rmdocherty/CPL-Imager/rotator.py

#!/usr/bin/env python3
# -*- coding: utf-8 -*-
"""
Created on Fri Aug  6 14:33:00 2021

@author: ronan
"""
#from pyftdi.ftdi import Ftdi
#import pyftdi.serialext
from time import sleep
import serial
from math import floor

PULSES_PER_DEGREE = 262144 / 360 #defined in docs
OFFSET_DEGREES = 1.7578125
#old values, H=11.7, V=60.7
HORIZONTAL = 11.7
VERTICAL = 60.7

class Rotator():
    """
    Rotator.

    Class to interface with ELL14 Thorlabs piezo rotation mount. Assumes the
    use of an R232 interface over a USB cable so can use pySerial. Docs says to
    just send ASCII strings for commands to use Serial.write().
    NB MUST TYPE "sudo chmod 666 /dev/ttyUSB0" to get permission to run.
    """

    def __init__(self, port): #might need to add flushing and setting params
        self.rot_count = 0
        connected = False
        try:
            #can just use pyserial to interface though may need to download drivers if on windows
            self._port = port #serial.Serial(port, baudrate=9600) #port='ftdi://ftdi:ft-x:DK0AJJZI/1'
            connected = True
        except Exception as error:
            print(f"Error: {error}, please supply a port.")
        if connected:
            sleep(0.05)
            self._port.reset_input_buffer()
            self._port.reset_output_buffer()
            sleep(0.05)
            self._home_motor() #reset pos
            self.set_jog_90()
            #self.rotate_to_angle(HORIZONTAL) #reset pos

    def _send_command(self, command, data=""):
        """
        Command structure is as follows:
            _____________________________________________________________________________________________
            |                    3 byte header            |                 8 byte data (optional)      |
            | 1 byte motor address (0-A) | 2 byte mneomic |       Hex number encoded as ASCII byte      |
            ¯¯¯¯¯¯¯¯¯¯¯¯¯¯¯¯¯¯¯¯¯¯¯¯¯¯¯¯¯¯¯¯¯¯¯¯¯¯¯¯¯¯¯¯¯¯¯¯¯¯¯¯¯¯¯¯¯¯¯¯¯¯¯¯¯¯¯¯¯¯¯¯¯¯¯¯¯¯¯¯¯¯¯¯¯¯¯¯¯¯¯¯¯
        I just use default motor address (0) - but no real justification.
        Mneomics available on data sheet, i.e 'ho' is home.
        Data not needed for some commands like home and jog, but is needed for move commands.
        """
        command_string = command + data
        command_byte = str.encode(command_string, encoding='ASCII')
        self._port.write(command_byte)

    def _freq_search(self):
        self._send_command("0s1")
        self._check_status()
        self._send_command("0us")

    def _optimize_motor(self):
        self._send_command("0om")
        self._check_status()

    def _home_motor(self):
        self._send_command("0ho1")

    def _set_jog_size(self, angle):
        set_angle_string = self._get_set_angle_string(angle)
        self._send_command("0sj", set_angle_string)
    
    def set_jog_90(self):
        self._send_command("0sj00008C00")

    def _get_offset(self):
        self._send_command("0go")
        offset_hex = self._port.readline()[2:]
        offset_hex_string = '0x' + str.encode(offset_hex)
        offset_int = int(offset_hex_string, base=16)
        offset_string = str(offset_int)
        print(f"Offset is {offset_string} degrees")

    def _get_set_angle_string(self, angle):
        """Convert angle to # of pulses and convert that to hex string."""
        pulses = floor(angle * 398.2222222) #should i use floor or ceil?
        int_string = hex(pulses)[2:].zfill(8)
        print(angle, int_string)
        return int_string.upper()

    def _send_get_status(self):
        self._send_command("0gs")

    def _check_status(self):
        done = False
        while done is False:
            self._send_get_status()
            data = self._port.readline()
            if data.decode()[:5] == "0GS00":
                done = True
            else:
                pass
        return 0

    def _check_angle(self):
        """Get device status until it returns the correct code (APO + pos in hex, specified in docs)."""
        rotated = False
        while rotated is False: #block until device says has rotated to specified angle
            data = self._port.readline()
            if data.decode()[:3] == "0PO": #0PO is return code for sucessful move command
                angle_str_hex = data.decode()[3:]
                #print(angle_str_hex)
                angle_dec = int(angle_str_hex, base=16)
                if angle_dec > 100000:
                    angle_dec = -1 * ((2**32) - angle_dec)
                angle = angle_dec / 398.22222222
                #print(f"{angle}")
                self.rot_count += 1
                rotated = True
            else:
                pass
        return 0

    def rotate_to_angle(self, angle):
        """Send rotate command and wait until device rotated."""
        set_angle_str = self._get_set_angle_string(angle)
        self._send_command("0ma", data=set_angle_str)
        self._check_angle()
        return 0
    
    def rotate_to_0(self):
        self._send_command("0ma00000000")
        self._check_angle()
        return 0
    
    def rotate_to_45(self):
        self._send_command("0ma00004600")
        self._check_angle()
        return 0
    
    def rotate_to_90(self):
        self._send_command("0ma00008C00")
        self._check_angle()
        return 0

    def jog_forward(self):
        self._send_command("0fw")
        self._check_angle()
        return 0

    def jog_backward(self):
        self._send_command("0bw")
        self._check_angle()
        return 0

    def rotate_by_angle(self, angle):
        set_angle_str = self._get_set_angle_string(angle)
        self._send_command("0mr", data=set_angle_str)
        self._check_angle()
        return 0
